Pyro61/Smart-weather-clock/Src/hw/external_hw/HD44780/HD44780.c

#include "HD44780.h"
#include "../../mcu_hw/gpio/gpio.h"
#include "../../../safe_state/safe_state.h"
#include "../../mcu_hw/tim/tim.h"
#include <stdint.h>
#include <stdbool.h>


/* Display size */
#define DISPLAY_ROWS    4
#define DISPLAY_COLS    20

/* GPIO ports and pins */
#define HD44780_RS      PORT_B, 12
#define HD44780_RW      PORT_B, 11
#define HD44780_E       PORT_B, 2
#define HD44780_D4      PORT_C, 5 // było pa10
#define HD44780_D5      PORT_C, 4
#define HD44780_D6      PORT_A, 7 //BYŁO PA15
#define HD44780_D7      PORT_A, 6 //BYŁO PC12 //ZMIANA PINÓW BO NA PCB NIE CHCIAŁO PASOWAĆ, TERAZ SIĘ ZGADZA Z TYM CO NA PCB

/* Control pins enable/disable */
#define RS_HIGH()       gpio_output_write(HD44780_RS, HIGH)
#define RS_LOW()        gpio_output_write(HD44780_RS, LOW)
#define RW_HIGH()       gpio_output_write(HD44780_RW, HIGH)
#define RW_LOW()        gpio_output_write(HD44780_RW, LOW)
#define E_HIGH()        gpio_output_write(HD44780_E, HIGH)
#define E_LOW()         gpio_output_write(HD44780_E, LOW)

/* Commands */
#define CMD_CLEAR       0x01
#define CMD_MOVE        0x80

/* Busy flag */
#define BUSY_FLAG       0x80


/* Rows addresses */
static uint8_t rows_addr[DISPLAY_ROWS] = {0x00, 0x40, 0x14, 0x54};

/* Current position holders */
static uint8_t row, col;

/* Helper function declarations */
static void set_data_gpio_as_input(void);
static void set_data_gpio_as_output(void);
static void send_4_bits(uint8_t data);
static void send_char(uint8_t c);
static void send_cmd(uint8_t cmd);
static uint8_t read_4_bits(void);
static uint8_t read_byte(void);
static bool is_lcd_free(void);
static bool is_current_position_correct(uint8_t c, uint8_t r);
static void change_position(const uint8_t c, const uint8_t r);


/* HD44780 functions */
void HD44780_init(void)
{
    if (gpio_config(HD44780_RS, OUTPUT, PUSH_PULL, NO_PULL, SPEED_MEDIUM) == ERR) safe_state();
    if (gpio_config(HD44780_RW, OUTPUT, PUSH_PULL, NO_PULL, SPEED_MEDIUM) == ERR) safe_state();
    if (gpio_config(HD44780_E, OUTPUT, PUSH_PULL, NO_PULL, SPEED_MEDIUM) == ERR) safe_state();
    set_data_gpio_as_output();

    RS_LOW();
    RW_LOW();
    E_LOW();
    delay_ms(50); /* Wait for power up */

    /* Configure display */
    send_4_bits(0x03);
	delay_ms(5);
	send_4_bits(0x03);
	delay_ms(1);
	send_4_bits(0x03);
	delay_ms(1);
	send_4_bits(0x02);
	delay_ms(1);
    send_cmd(0x28); /* 4-bit mode, 2 lines, 5x8 font */
    send_cmd(0x0C); /* Display on, cursor and blink off */
    send_cmd(0x06); /* Increment cursor position, no display shift */
    send_cmd(CMD_CLEAR); /* Clear the display */

    delay_ms(2); /* Wait for stabilisation */
}


static void HD44780_print(const char *buf)
{
    /* Set current position to 0,0 */
    col = 0;
    row = 0;
    change_position(col, row);

    while (*buf)
    {
        /* Check writing position and eventually change it */
        if (is_current_position_correct(col, row) != true)
        {
            change_position(col, row);
        }

        /* New line */
        if (*buf == '\n')
        {
            /* Line already changed */
            if (col == 0)
            {
                buf++;
                continue;
            }

            row++;
            col = 0;
            buf++;
            change_position(col, row);
            continue;
        }

        /* Char send */
        send_char(*buf++);
        col++;
    }
}


static void HD44780_clear(void)
{
    send_cmd(CMD_CLEAR);
    row = 0;
    col = 0;
    delay_ms(2); /* Without it first line is cut */
}


/* Return API functions */
const struct display_interface HD44780_funs = 
{
    HD44780_init,
    HD44780_print,
    HD44780_clear,
};


const struct display_interface *HD44780_get_funs(void)
{
    return &HD44780_funs;
}


/* Helper function definitions */
static void set_data_gpio_as_input(void)
{
    if (gpio_config(HD44780_D4, INPUT, PUSH_PULL, NO_PULL, SPEED_MEDIUM) == ERR) safe_state();
    if (gpio_config(HD44780_D5, INPUT, PUSH_PULL, NO_PULL, SPEED_MEDIUM) == ERR) safe_state();
    if (gpio_config(HD44780_D6, INPUT, PUSH_PULL, NO_PULL, SPEED_MEDIUM) == ERR) safe_state();
    if (gpio_config(HD44780_D7, INPUT, PUSH_PULL, NO_PULL, SPEED_MEDIUM) == ERR) safe_state();
}


static void set_data_gpio_as_output(void)
{
    if (gpio_config(HD44780_D4, OUTPUT, PUSH_PULL, NO_PULL, SPEED_MEDIUM) == ERR) safe_state();
    if (gpio_config(HD44780_D5, OUTPUT, PUSH_PULL, NO_PULL, SPEED_MEDIUM) == ERR) safe_state();
    if (gpio_config(HD44780_D6, OUTPUT, PUSH_PULL, NO_PULL, SPEED_MEDIUM) == ERR) safe_state();
    if (gpio_config(HD44780_D7, OUTPUT, PUSH_PULL, NO_PULL, SPEED_MEDIUM) == ERR) safe_state();
}


static void send_4_bits(uint8_t data)
{
    E_HIGH();
    gpio_output_write(HD44780_D4, (data & 0x01) ? 1 : 0);
    gpio_output_write(HD44780_D5, (data & 0x02) ? 1 : 0);
    gpio_output_write(HD44780_D6, (data & 0x04) ? 1 : 0);
    gpio_output_write(HD44780_D7, (data & 0x08) ? 1 : 0);
    E_LOW();
}


static void send_char(uint8_t c)
{
    while (!is_lcd_free());
    RS_HIGH();
    RW_LOW();
    set_data_gpio_as_output();

    send_4_bits(c >> 4);
    send_4_bits(c);
}


static void send_cmd(uint8_t cmd)
{
    while (!is_lcd_free());
    RS_LOW();
    RW_LOW();
    set_data_gpio_as_output();

    send_4_bits(cmd >> 4);
    send_4_bits(cmd);
}


static uint8_t read_4_bits(void)
{
    uint8_t tmp;

    E_HIGH();
    tmp = (gpio_input_read(HD44780_D4) << 0);
    tmp |= (gpio_input_read(HD44780_D5) << 1);
    tmp |= (gpio_input_read(HD44780_D6) << 2);
    tmp |= (gpio_input_read(HD44780_D7) << 3);
    E_LOW();

    return tmp;
}


static uint8_t read_byte(void)
{
    uint8_t tmp;
    set_data_gpio_as_input();

    RW_HIGH();

    tmp = (read_4_bits() << 4);
    tmp |= read_4_bits();

    return tmp;
}


static bool is_lcd_free(void)
{
    uint8_t tmp;
    RS_LOW();

    tmp = read_byte();
    if (tmp & BUSY_FLAG) return false;
    else return true;
}


/* Returns true if there's no need to change current position
 * False if col/row has reached boundaries */
static bool is_current_position_correct(uint8_t c, uint8_t r)
{
    bool tmp = true;

    /* Columns */
    if (c >= DISPLAY_COLS)
    {
        col = 0;
        row++;
        tmp = false;
    }

    /* Rows */
    if (r >= DISPLAY_ROWS)
    {
        col = 0;
        row = 0;
        tmp = false;
    }

    return tmp;
}


static void change_position(const uint8_t c, const uint8_t r)
{
    if ((c >= DISPLAY_COLS) || (r >= DISPLAY_ROWS)) return; /* Wrong column / row */

    send_cmd(CMD_MOVE | (rows_addr[r] + c));
}
