Pyro61/Smart-weather-clock/Src/hw/mcu_hw/spi/spi.c

#include "spi.h"
#include "stm32g4xx.h"
#include "../gpio/gpio.h"
#include "../../../safe_state/safe_state.h"
#include <stdlib.h>


enum spi_state
{
    SPI_ERR = -1,
    SPI_FREE = 0,
    SPI_BUSY = 1,
    SPI_NOT_INITIALIZED = 2
};


/* Callback address holder */
cb_t recv_callback;

/* SPI1 state holder */
enum spi_state spi1_state = SPI_NOT_INITIALIZED;


void spi1_init(void)
{
    /* Enable SPI clock */
	RCC -> APB2ENR |= RCC_APB2ENR_SPI1EN;

    /* Spi configuration 
     * 8 bit data size, Motorola format */
	SPI1 -> CR1 |= 0x04 << 3; /* Baudrate - freq / 32 = 1,5 MHz */
	SPI1 -> CR1 |= SPI_CR1_MSTR; /* Master mode */
	SPI1 -> CR1 |= (SPI_CR1_SSM | SPI_CR1_SSI); /* Software SS */

	/* GPIO config - PA5 - SCK, PA6 - MISO, PA7 - MOSI */
	if (gpio_config(PORT_A, 5, ALTERNATE_FUN, PUSH_PULL, NO_PULL, SPEED_VERY_HIGH) == ERR) safe_state();
    if (gpio_set_af(PORT_A, 5, 5) == ERR) safe_state();
    if (gpio_config(PORT_A, 6, ALTERNATE_FUN, PUSH_PULL, NO_PULL, SPEED_VERY_HIGH) == ERR) safe_state();
    if (gpio_set_af(PORT_A, 6, 5) == ERR) safe_state();
    if (gpio_config(PORT_A, 7, ALTERNATE_FUN, PUSH_PULL, NO_PULL, SPEED_VERY_HIGH) == ERR) safe_state();
    if (gpio_set_af(PORT_A, 7, 5) == ERR) safe_state();

    /* DMA config */
    /* Enable DMA1 and DMAMUX clocks */
    RCC -> AHB1ENR |= RCC_AHB1ENR_DMA1EN | RCC_AHB1ENR_DMAMUX1EN;
    /* Receive
	 * Periph addr, priority, memory and periph sizes, mem inc mode, transfer complete and error IRQ, DMA request source */
	DMA1_Channel1 -> CPAR = (uint32_t)&(SPI1 -> DR);
	DMA1_Channel1 -> CCR |= DMA_CCR_PL_0 | DMA_CCR_MINC | DMA_CCR_TEIE | DMA_CCR_TCIE;
    NVIC_SetPriority(DMA1_Channel1_IRQn, 10); /* Set low priority because inside irq callback fun is called */
	NVIC_EnableIRQ(DMA1_Channel1_IRQn);
    DMAMUX1_Channel0 -> CCR |= 0x0A << 0;

	/* Enable SPI */
	SPI1 -> CR1 |= SPI_CR1_SPE;

    spi1_state = SPI_FREE;
}


/* Returns if spi1 is ready to use */
bool is_spi1_bus_free(void)
{
    if (spi1_state == SPI_FREE)
    {
        return true;
    }

    else
    {
        return false;
    }
}


/* SPI master transmit */
void spi1_write_polling(uint8_t reg, uint8_t *data, uint8_t bytes_num)
{
    /* Mechanism blocking using spi when it's not ready to use */
    if (spi1_state != SPI_FREE)
    {
        return;
    }

    spi1_state = SPI_BUSY;
    uint8_t i;

    /* Send register address to slave */
    *(volatile uint8_t *)&SPI1 -> DR = reg;
    
    /* Send data */
    for (i = 0; i < bytes_num; i++)
    {
        while (!(SPI1 -> SR & SPI_SR_TXE)); /* Wait for transmit buffer to be not full */
        *(volatile uint8_t *)&SPI1 -> DR = data[i];
    }

    spi1_state = SPI_FREE;
}


/* SPI master receive */
void spi1_read_dma(uint8_t reg, uint8_t *buf, uint8_t bytes_num, cb_t cb)
{
    /* Mechanism blocking using spi when it's not ready to use */
    if (spi1_state != SPI_FREE)
    {
        return;
    }

    spi1_state = SPI_BUSY;

    /* Write callback address */
    recv_callback = cb;

    /* DMA settings */
    SPI1 -> CR2 |= SPI_CR2_RXDMAEN;
	DMA1_Channel1 -> CNDTR = bytes_num;
	DMA1_Channel1 -> CMAR = (uint32_t)buf;
    DMA1_Channel1 -> CCR |= DMA_CCR_EN;

    /* Send register address to slave */
    *(volatile uint8_t *)&SPI1 -> DR = reg;
}


/* DMA reception finished */
void DMA1_CH1_IRQHandler(void)
{
	/* SPI1 RX DMA reception finished */
	if (DMA1 -> ISR & DMA_ISR_TCIF1)
	{
		/* Delete half and full complete transfer flags */
		DMA1 -> IFCR = DMA_IFCR_CTCIF1 | DMA_IFCR_CHTIF1;

		/* Disable DMA CH1 */
		DMA1_Channel1 -> CCR &= ~DMA_CCR_EN;

		/* Disable SPI1 RX DMA mode */
		SPI1 -> CR2 &= ~SPI_CR2_RXDMAEN;

        /* Change SPI1 state variable */
        spi1_state = SPI_FREE;

		/* Reception end callback function call */
        if (recv_callback != NULL)
        {
            recv_callback();
        }
	}
}
